NYH32O99E1Lg/SmartCubeV1/hardware/pictures/batt3.jpg

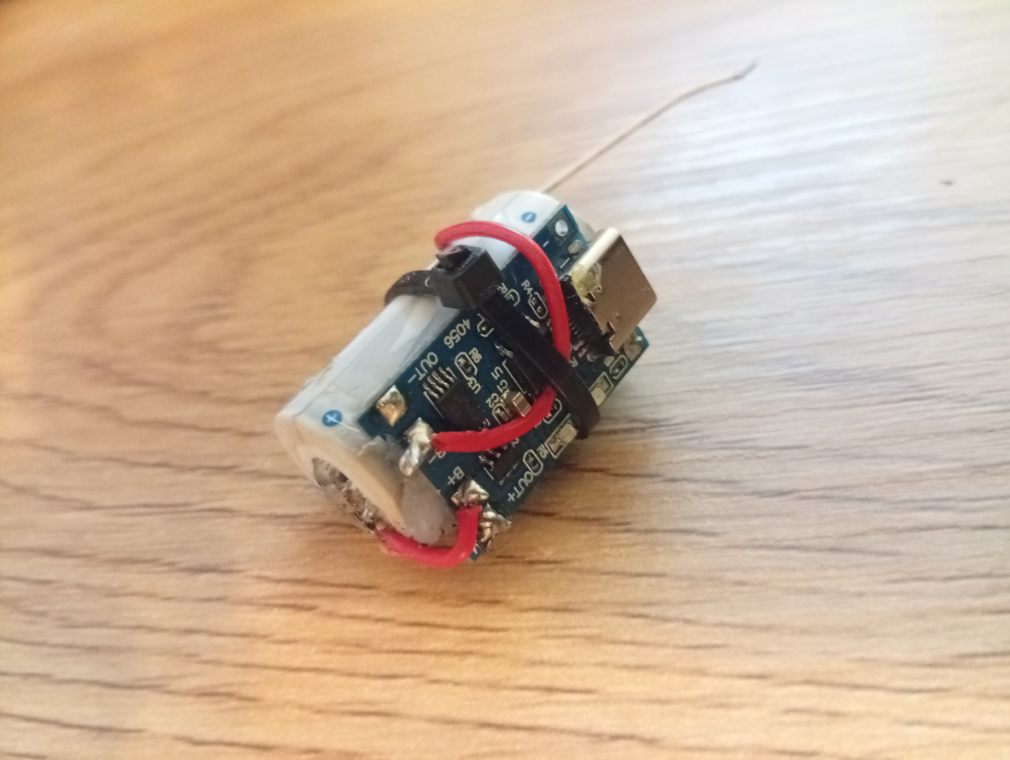
hardware/pictures/batt3.jpg
