NYH32O99E1Lg/SmartCubeV1/hardware/pictures/IMG_0052.jpg

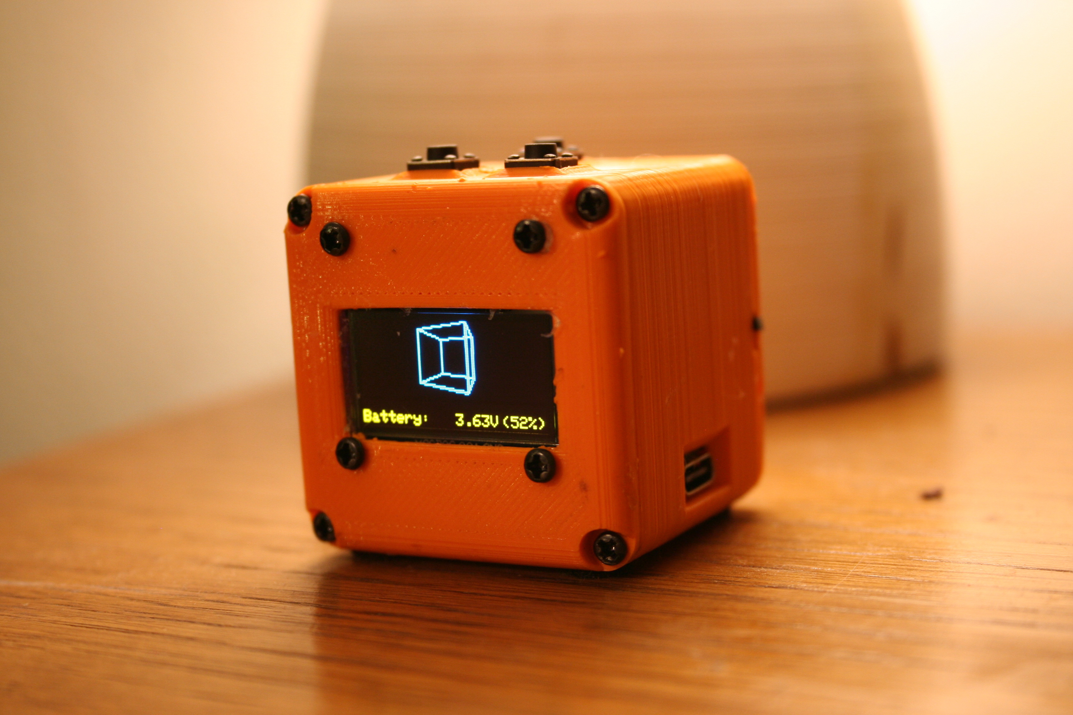
hardware/pictures/IMG_0052.jpg
