NYH32O99E1Lg/SmartCubeV1/hardware/pictures/IMG_0053.jpg

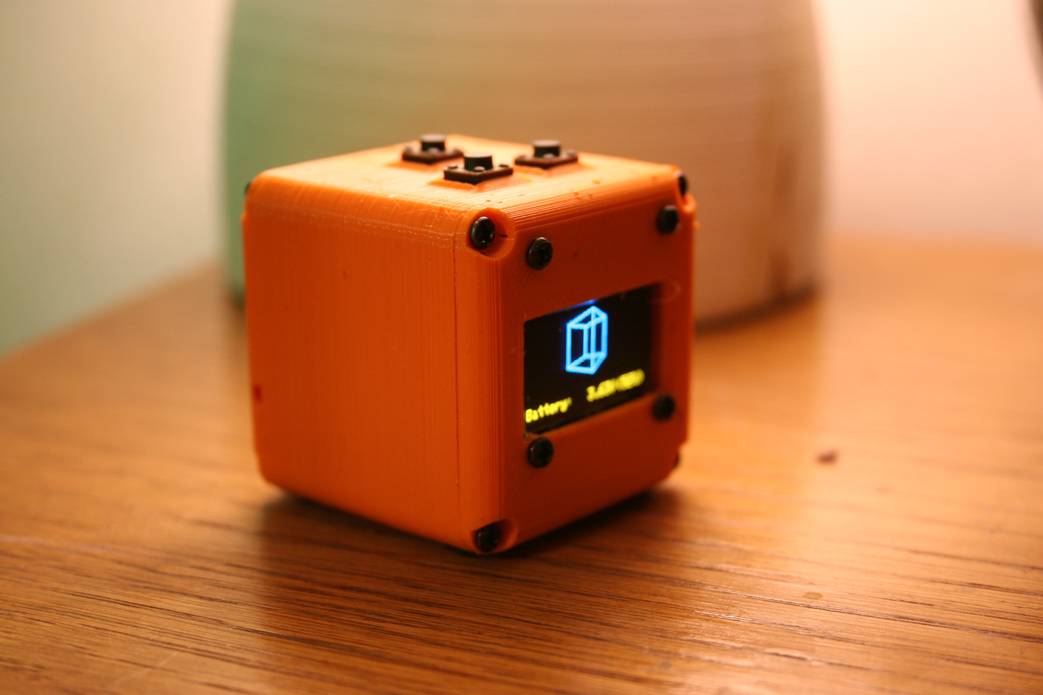
hardware/pictures/IMG_0053.jpg
