NYH32O99E1Lg/SmartCubeV1/hardware/pictures/IMG_20240618_203812.jpg

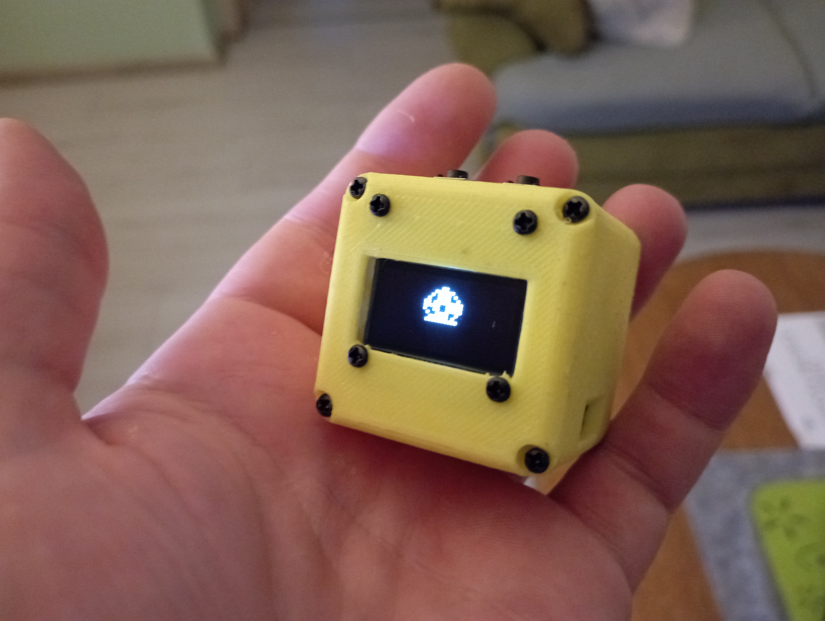
hardware/pictures/IMG_20240618_203812.jpg
