NYH32O99E1Lg/SmartCubeV1/hardware/pictures/IMG_20241022_073144.jpg

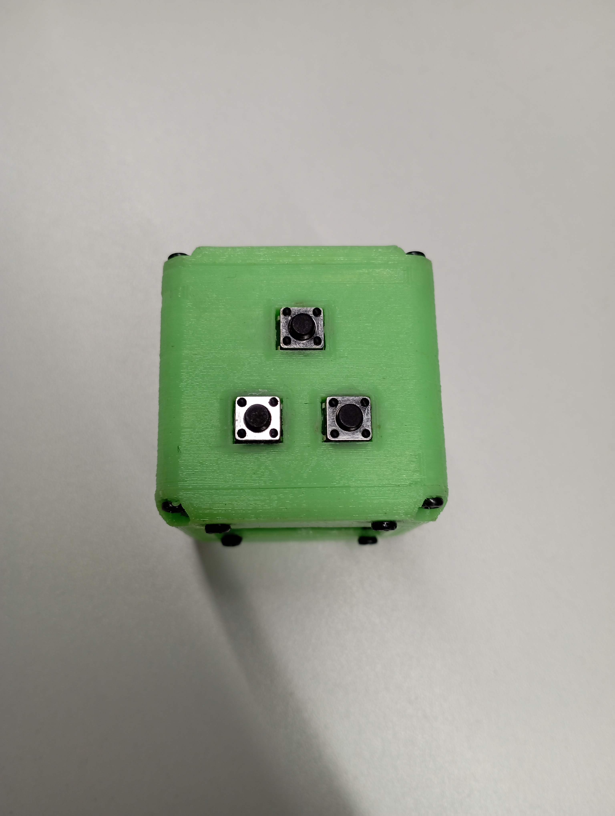
hardware/pictures/IMG_20241022_073144.jpg
