NYH32O99E1Lg/SmartCubeV1/hardware/pictures/platformio1.png

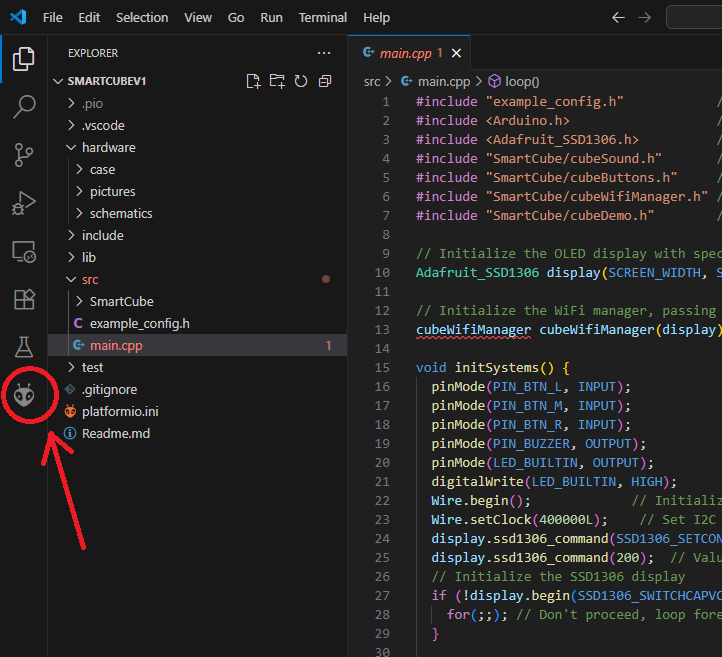
hardware/pictures/platformio1.png
