NYH32O99E1Lg/SmartCubeV1/hardware/schematics/schematic1.png

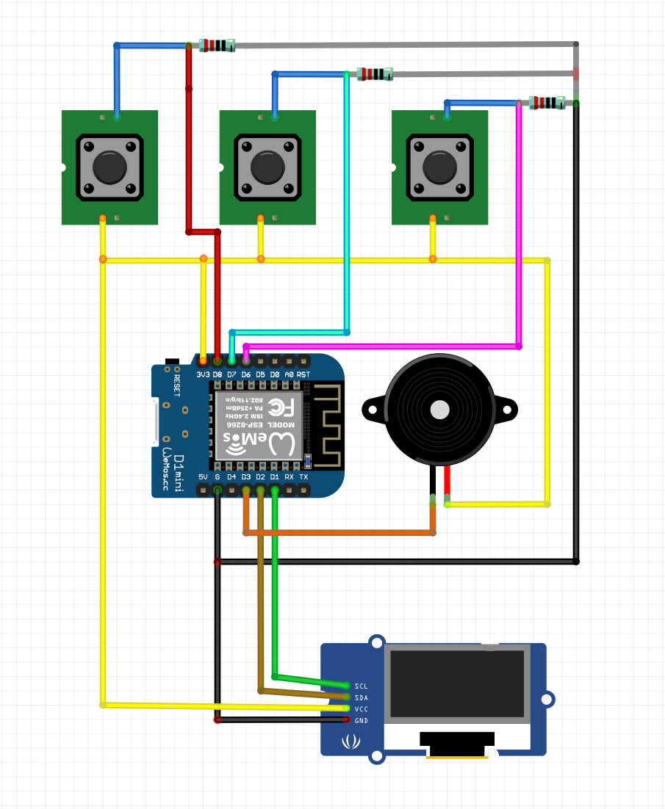
hardware/schematics/schematic1.png
