NYH32O99E1Lg/SmartCubeV1/hardware/schematics/schematic2.png

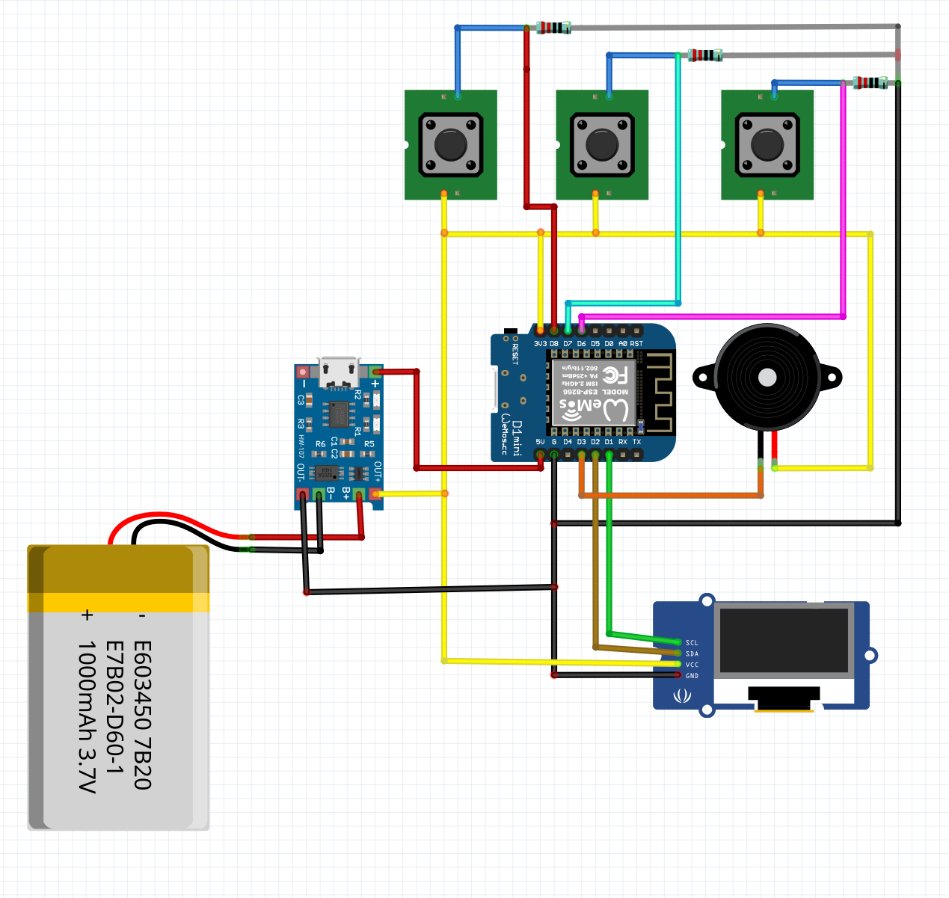
hardware/schematics/schematic2.png
