NYH32O99E1Lg/SmartCubeV1/hardware/schematics/schematic3.png

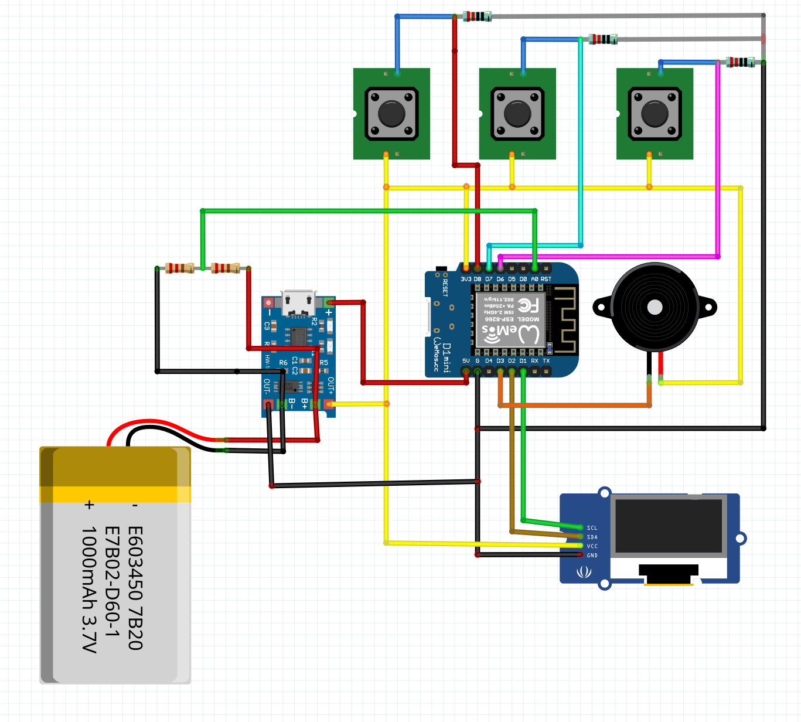
hardware/schematics/schematic3.png
