NYH32O99E1Lg/SmartCubeV1/hardware/pictures/build1.jpg

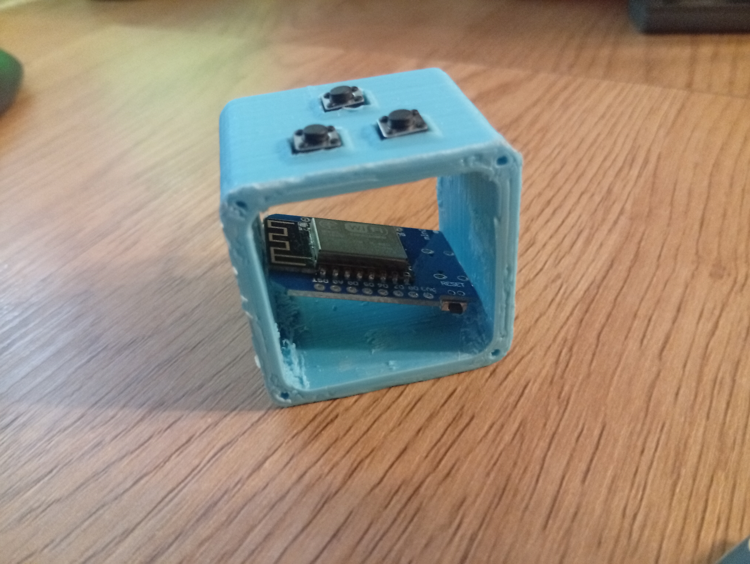
hardware/pictures/build1.jpg
