NYH32O99E1Lg/SmartCubeV1/hardware/pictures/build2.jpg

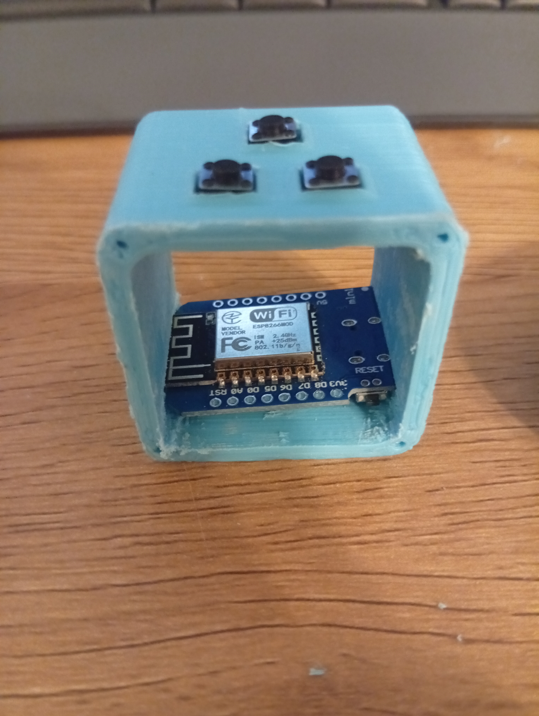
hardware/pictures/build2.jpg
