NYH32O99E1Lg/SmartCubeV1/hardware/pictures/build3.jpg

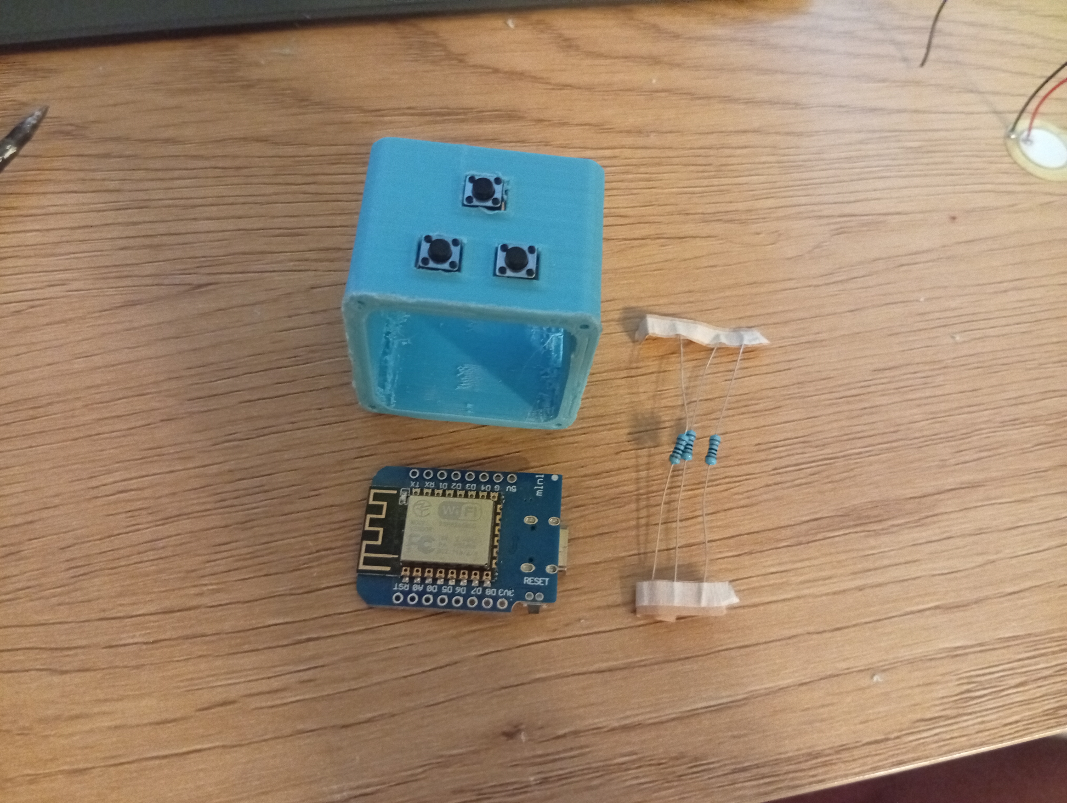
hardware/pictures/build3.jpg
