NYH32O99E1Lg/SmartCubeV1/hardware/pictures/build4.jpg

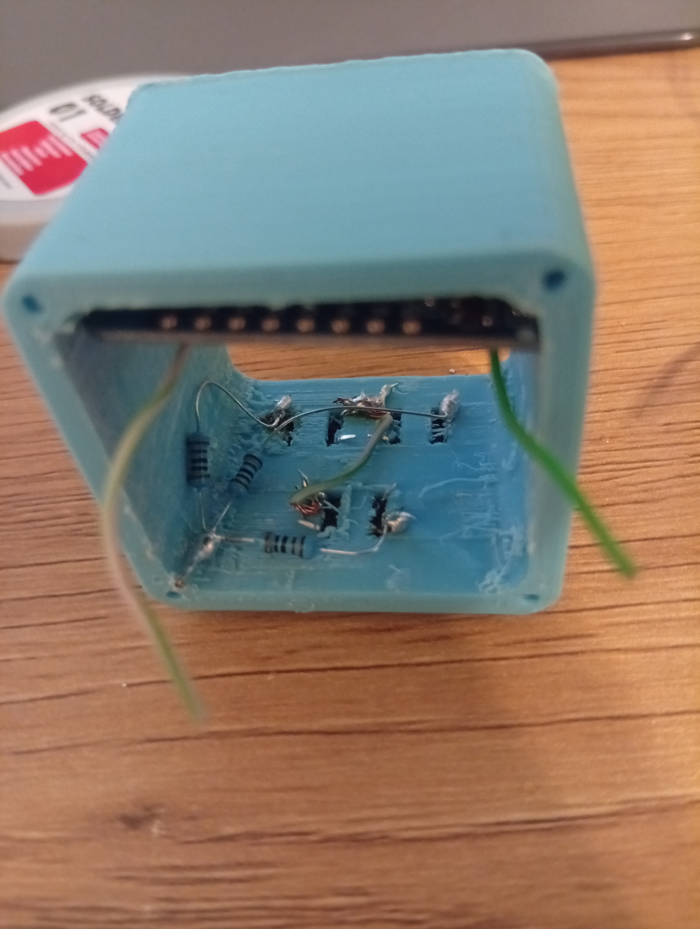
hardware/pictures/build4.jpg
