NYH32O99E1Lg/SmartCubeV1/hardware/pictures/build5.jpg

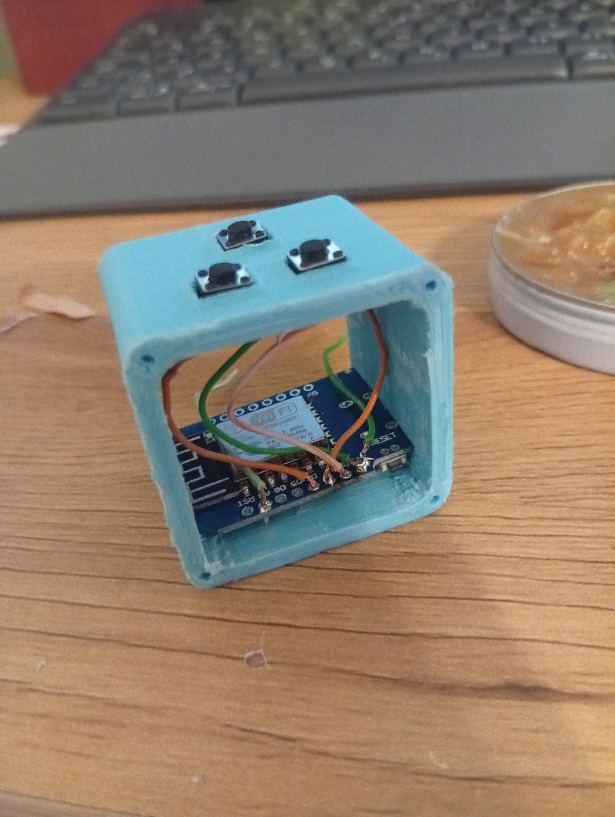
hardware/pictures/build5.jpg
