NYH32O99E1Lg/SmartCubeV1/hardware/pictures/build6.jpg

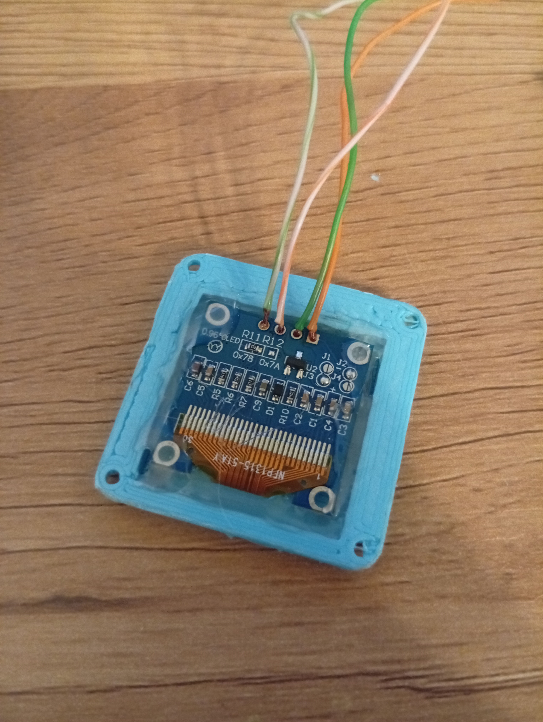
hardware/pictures/build6.jpg
