NYH32O99E1Lg/SmartCubeV1/hardware/pictures/build7.jpg

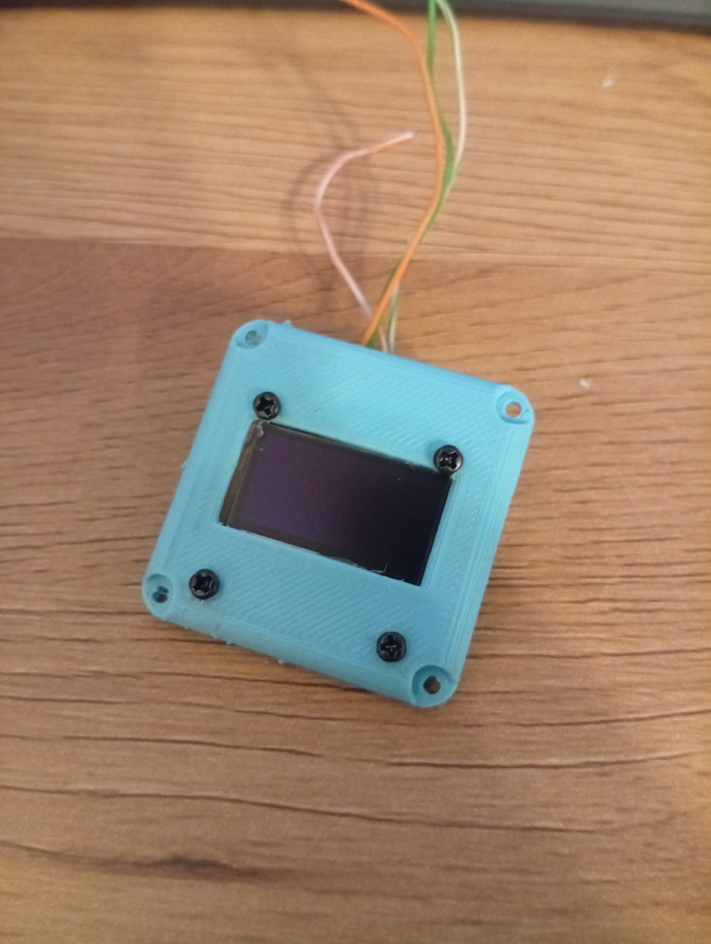
hardware/pictures/build7.jpg
