NYH32O99E1Lg/SmartCubeV1/hardware/pictures/IMG_20241213_171725.jpg

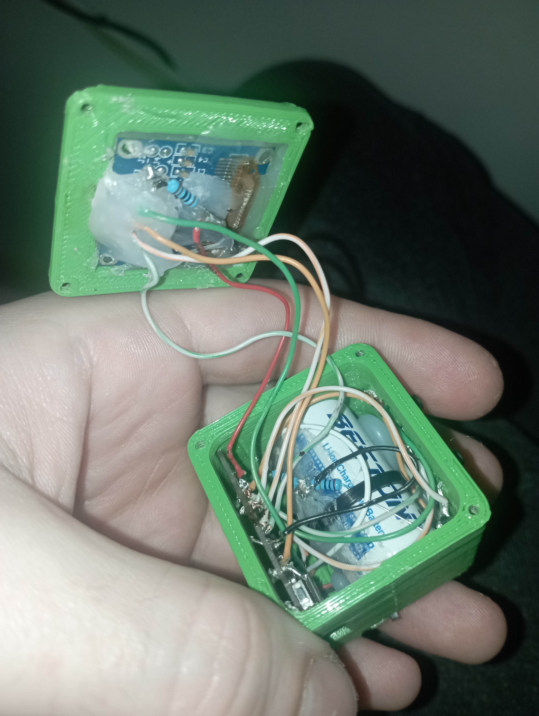
hardware/pictures/IMG_20241213_171725.jpg
